Tommie1236/pico-art-net-node/Code/src/firmware/dmx-test.cpp

#include <stdio.h>
#include "hardware/gpio.h"
#include "pico/stdlib.h"
#include "pico/time.h"

#include "hardware/adc.h"

#include "main.h"

#include <DmxOutput.h>

DmxOutput dmx;

uint8_t universe[UNIVERSE_LENGTH + 1];


int main () {

    adc_init();
    adc_gpio_init(26);
    adc_gpio_init(27);


    dmx.begin(0);
    universe[1] = 0;        // red
    universe[2] = 255;      // green
    universe[3] = 0;        // blue
    universe[4] = 0;        // white
    universe[5] = 100;      // dimmer


while (1) {
    dmx.write(universe, UNIVERSE_LENGTH);
    while (dmx.busy()) {}

    adc_select_input(0);
    universe[1] = adc_read() / 16;
    adc_select_input(1);
    universe[3] = adc_read() / 16;

}
};
